daisyaudio/Seed3-DevKit-Pedal/pcb/ES-Seed3-DevKit-Pedal-Rev1/review/ES-Seed3-DevKit-Pedal-Rev1-User_Drawings.pdf

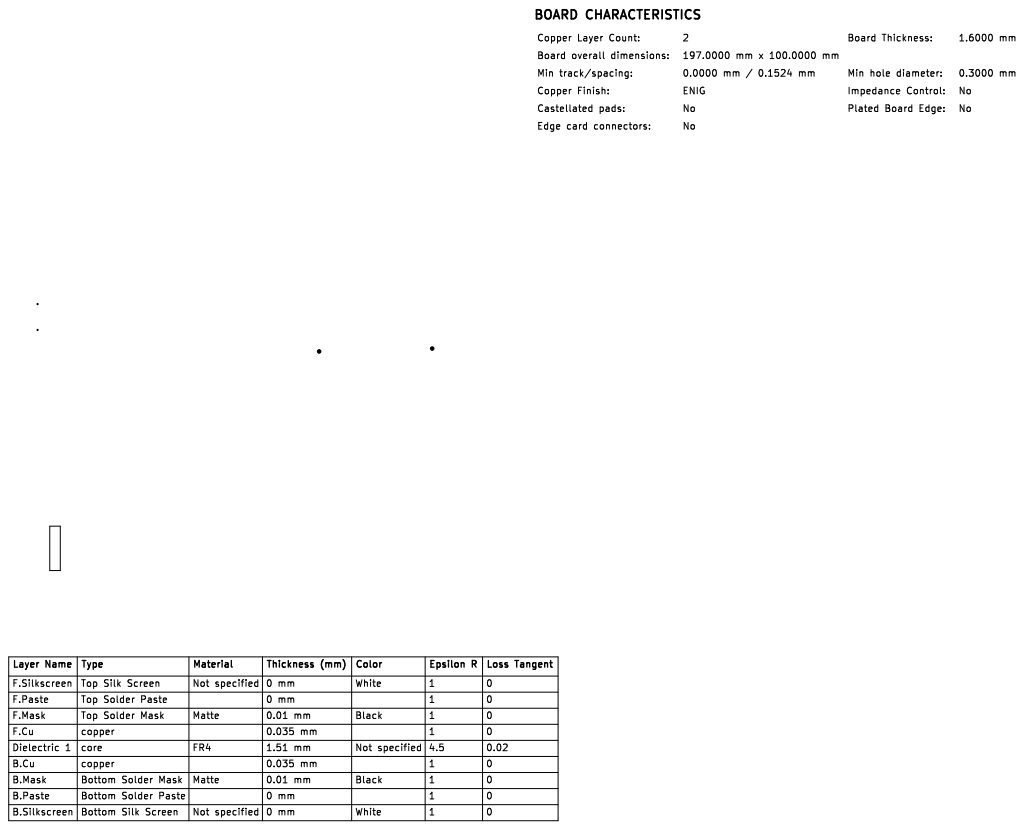
[picture p17: page 1]

No Matte Not specified

1 | copper Top Solder Screen Dielectric Mask Top Silk | Not specified | 0.01 mm | White | 1 F.Mask | Loss Tangent B.Paste

Type

core | | 1.51 mm 0 mm | Black Not specified Color | | R | 0.02 Epsilon

1 Matte

Bottom Solder Mask | | 0.035 mm | | 1 | 0 B.Cu 0
FR4 | | | | | | 4.5 | 0 Black B.Silkscreen

0 mm | | | 0 Bottom Solder Paste 0
