daisyaudio/Seed3-DevKit-Pedal/pcb/ES-Seed3-DevKit-Pedal-Rev3/review/2025-12-10/board/ES-Seed3-DevKit-Pedal-Rev3.pdf

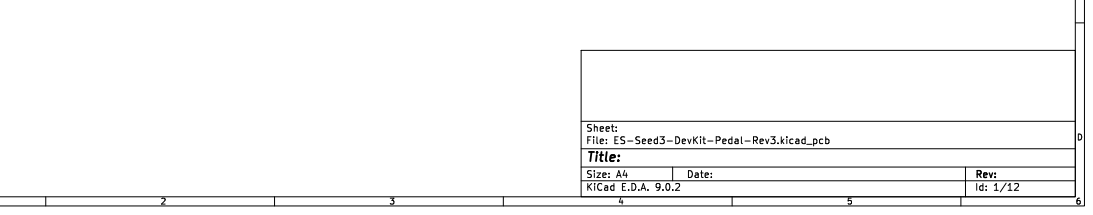
[picture p18: page 1]

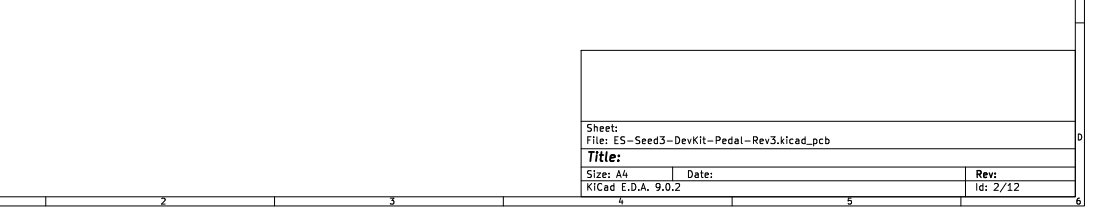
[picture p19: page 2]

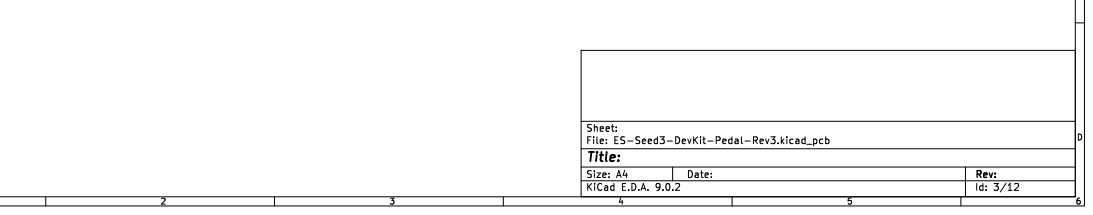
[picture p20: page 3]

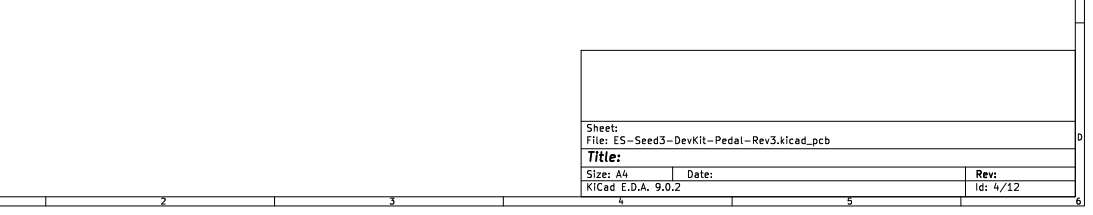
[picture p21: page 4]

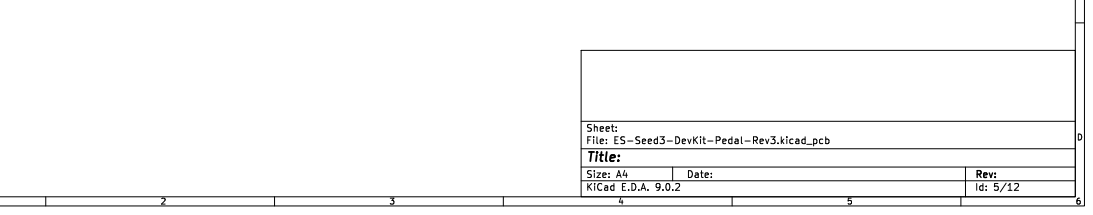
[picture p22: page 5]

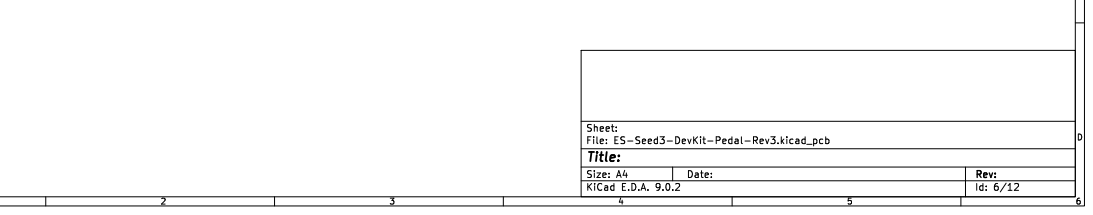
[picture p23: page 6]

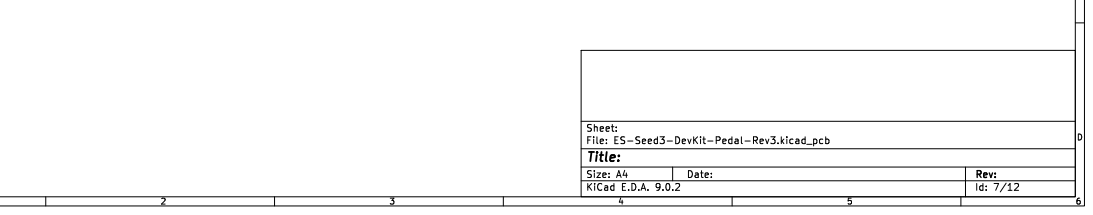
[picture p24: page 7]

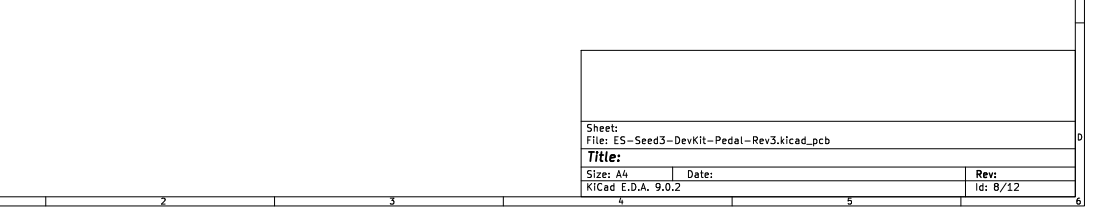
[picture p25: page 8]

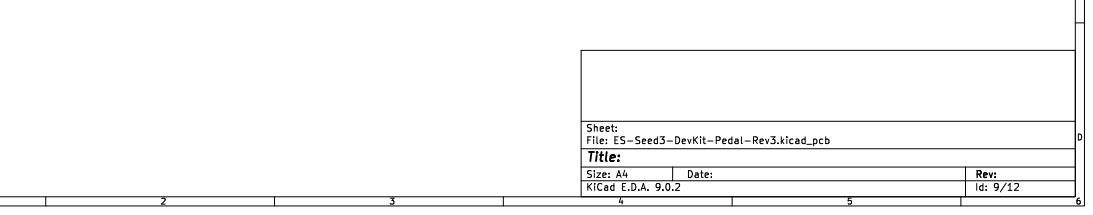
[picture p26: page 9]

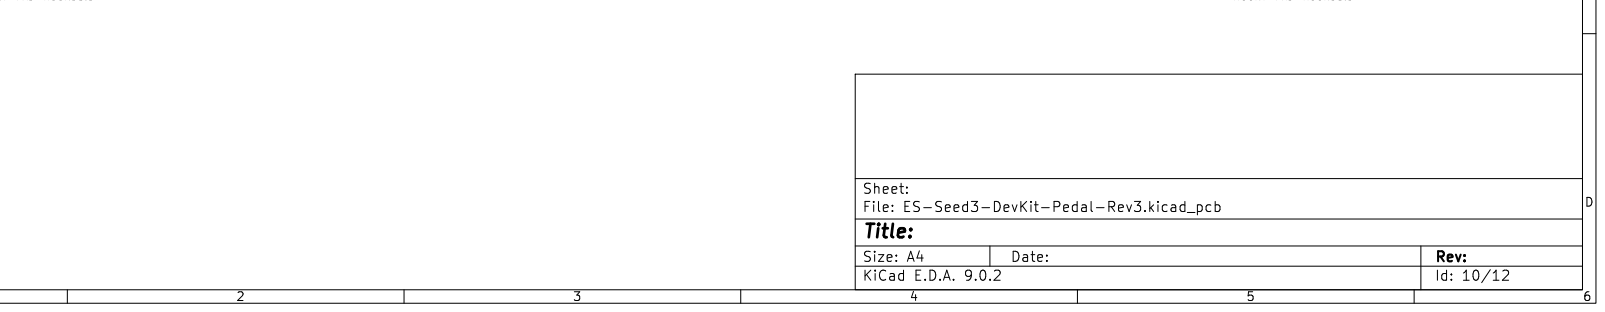
[picture p27: page 10]

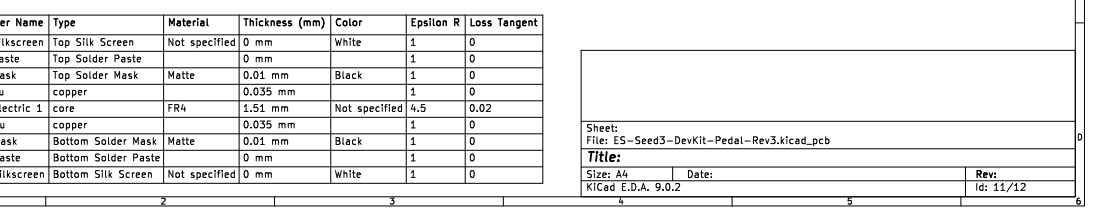
[picture p28: page 11]

0 Type

0 mm | Loss Tangent 0.02
0 mm | | 0

copper | Mask | | 0.01 mm 0.035 mm | 0 Top Solder 0 Not specified 0

Matte FR4 | 0.035 mm

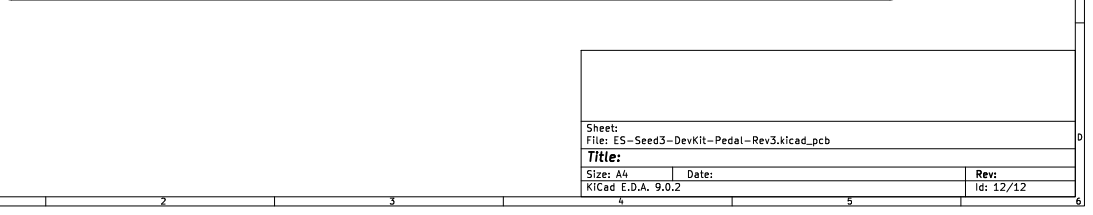
[picture p29: page 12]
