daisyaudio/Seed3-DevKit-Pedal/pcb/ES-Seed3-DevKit-Pedal-Rev2/review/2025-07-11/board/ES-Seed3-DevKit-Pedal-Rev2.pdf

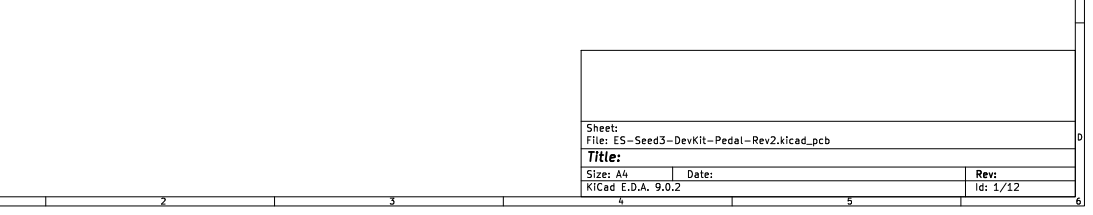
[picture p30: page 1]

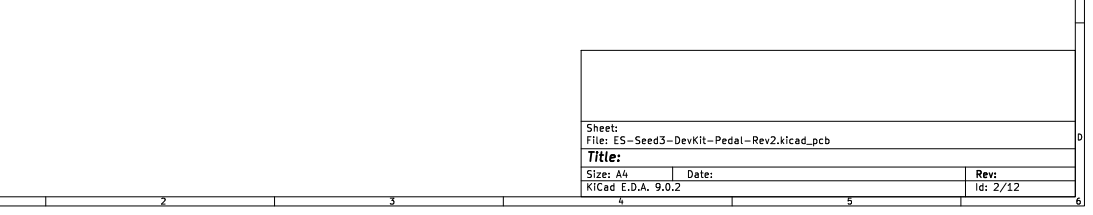
[picture p31: page 2]

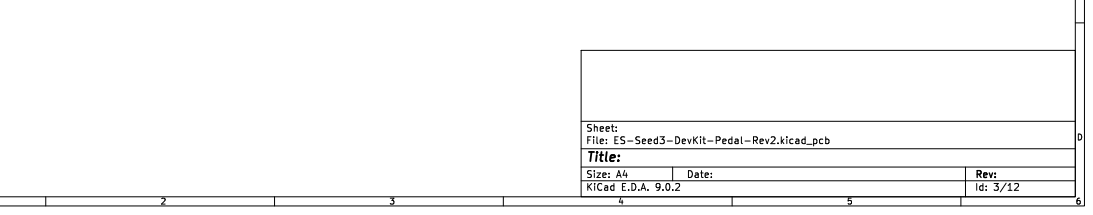
[picture p32: page 3]

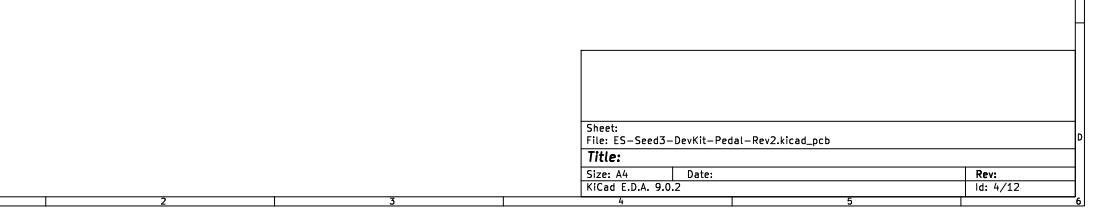
[picture p33: page 4]

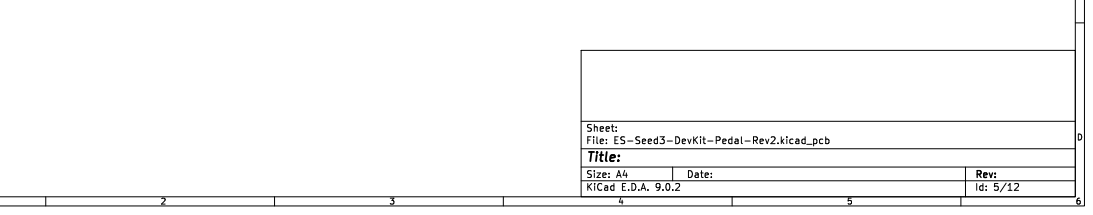
[picture p34: page 5]

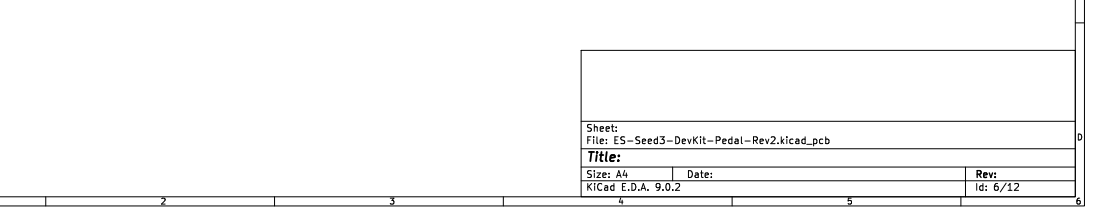
[picture p35: page 6]

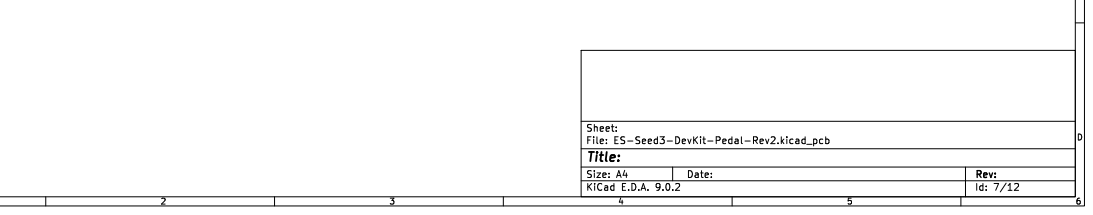
[picture p36: page 7]

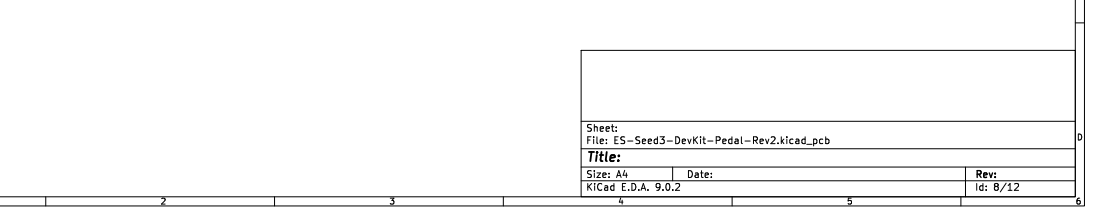
[picture p37: page 8]

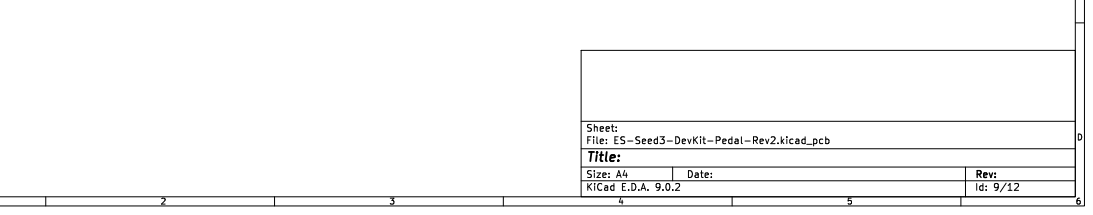
[picture p38: page 9]

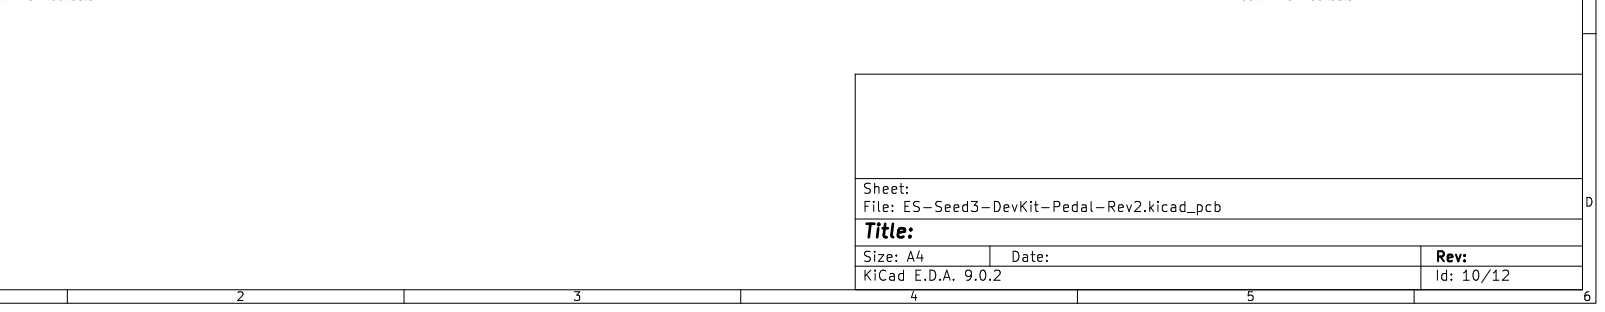
[picture p39: page 10]

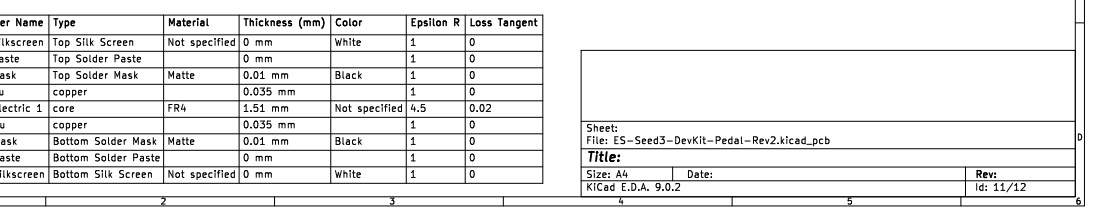
[picture p40: page 11]

Copper Layer Count: Not specified

Edge card connectors: Color

Mask | 0 mm | Loss Tangent 0.02 0 Top Solder

0 Type

Thickness (mm) | White
0 mm | | 0

copper | | 0.01 mm 0.035 mm | | 0

Black Bottom Solder Paste | | 4.5

Matte FR4 | 0.035 mm | 1 B.Silkscreen

0 Not specified

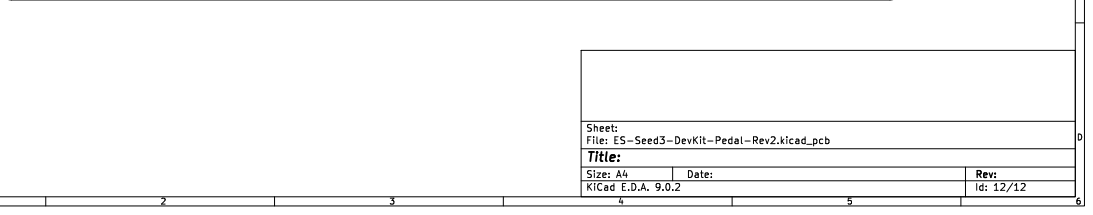
[picture p41: page 12]
